yuburoll/DASIC/V2-375u/images/dasicHeader.jpg

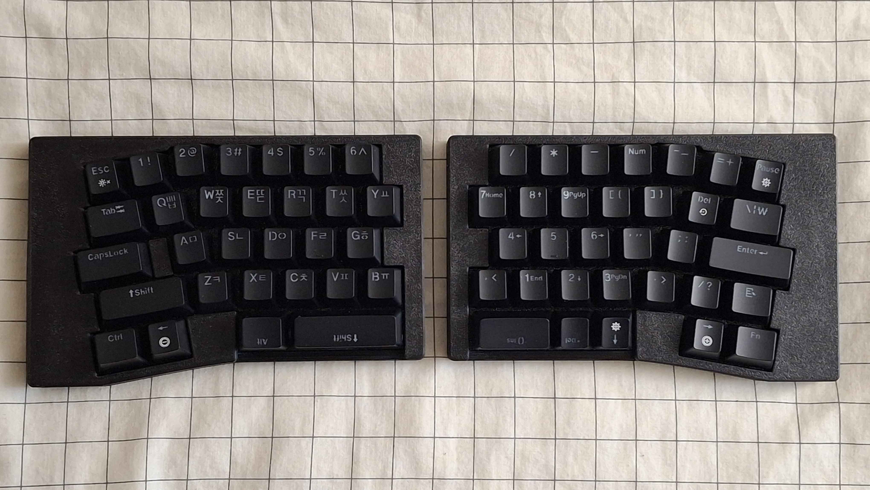
V2-375u/images/dasicHeader.jpg
