yuburoll/DASIC/V2-375u/images/dasicProfile.jpg

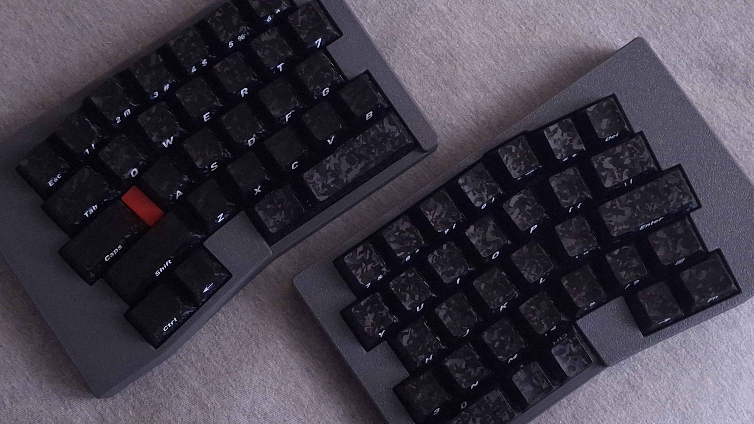
V2-375u/images/dasicProfile.jpg
