yuburoll/DASIC/V2-375u/images/dasicV2Pad.png

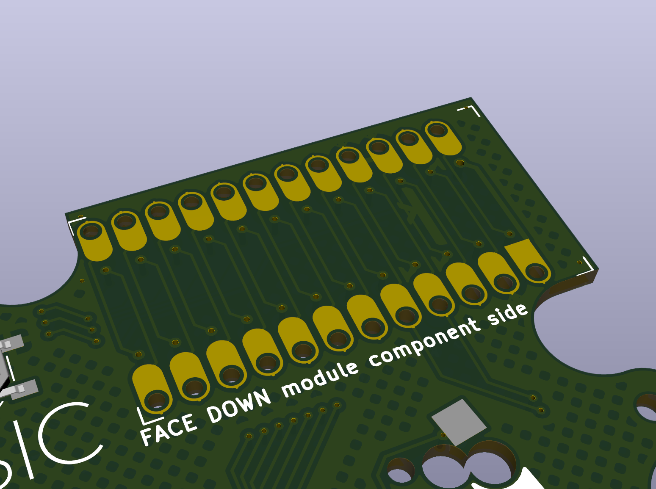
V2-375u/images/dasicV2Pad.png
