yuburoll/DASIC/V2-375u/kicad/dasic.kicad_sch

## KiCad design V2-375u/kicad/dasic.kicad_sch (2026-03-04)

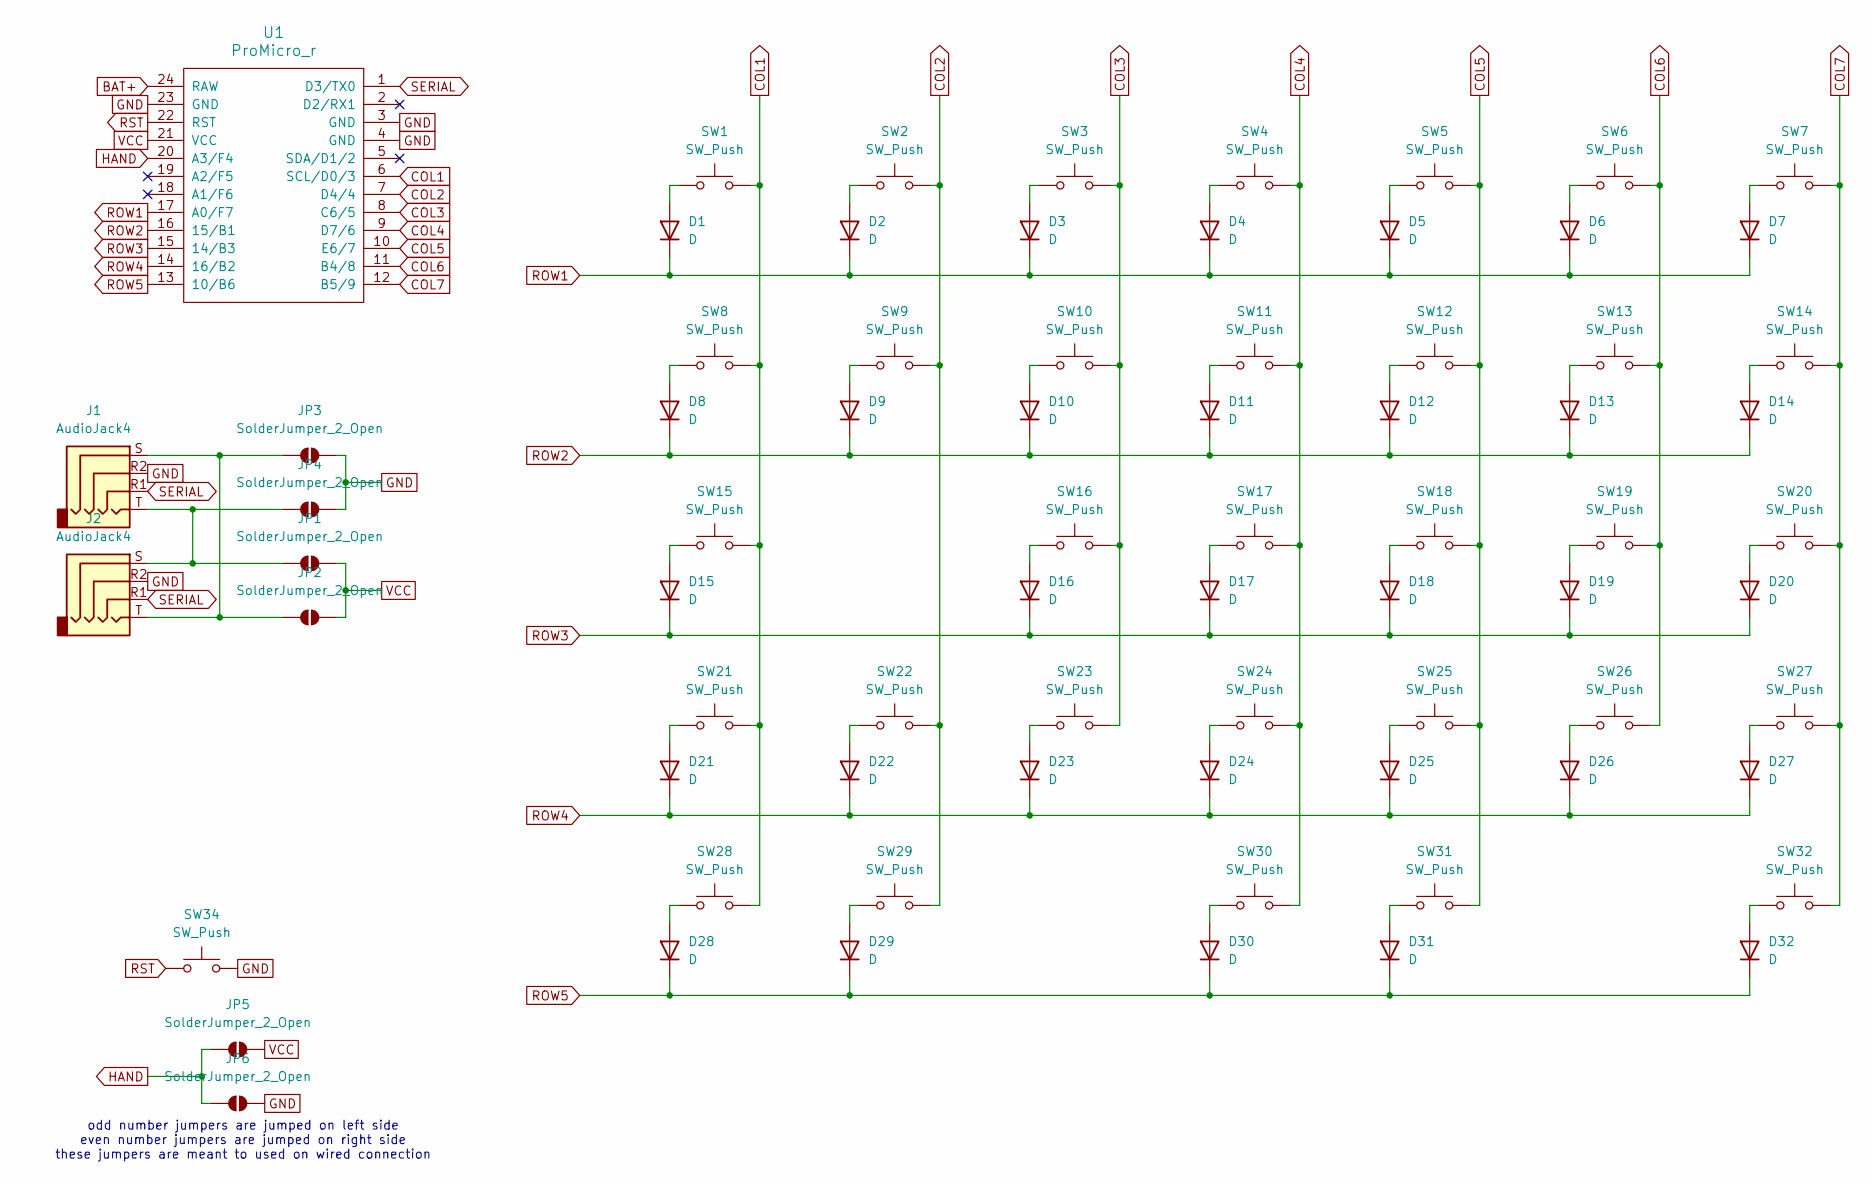
[picture p60: schematic dasic.kicad_sch]

Parts:
D1, D2, D3, D4, D5, D6, D7, D8, D9, D10, D11, D12, D13, D14, D15, D16, D17, D18, D19, D20, D21, D22, D23, D24, D25, D26, D27, D28, D29, D30, D31, D32: D
J1, J2: AudioJack4
JP1, JP2, JP3, JP4, JP5, JP6: SolderJumper_2_Open
SW1, SW2, SW3, SW4, SW5, SW6, SW7, SW8, SW9, SW10, SW11, SW12, SW13, SW14, SW15, SW16, SW17, SW18, SW19, SW20, SW21, SW22, SW23, SW24, SW25, SW26, SW27, SW28, SW29, SW30, SW31, SW32, SW34: SW_Push
U1: ProMicro_r

Connections:
BAT+: U1.24 (RAW)
COL1: SW1.2, SW8.2, SW15.2, SW21.2, SW28.2, U1.6 (SCL/D0/3)
COL2: SW2.2, SW9.2, SW22.2, SW29.2, U1.7 (D4/4)
COL3: SW3.2, SW10.2, SW16.2, SW23.2, U1.8 (C6/5)
COL4: SW4.2, SW11.2, SW17.2, SW24.2, SW30.2, U1.9 (D7/6)
COL5: SW5.2, SW12.2, SW18.2, SW25.2, SW31.2, U1.10 (E6/7)
COL6: SW6.2, SW13.2, SW19.2, SW26.2, U1.11 (B4/8)
COL7: SW7.2, SW14.2, SW20.2, SW27.2, SW32.2, U1.12 (B5/9)
GND: J1.R2, J2.R2, JP3.2 (B), JP4.2 (B), JP6.1 (A), SW34.2, U1.3 (GND), U1.4 (GND), U1.23 (GND)
HAND: JP5.2 (B), JP6.2 (B), U1.20 (A3/F4)
unnamed: D1.2 (A), SW1.1
unnamed: D2.2 (A), SW2.1
unnamed: D3.2 (A), SW3.1
unnamed: D4.2 (A), SW4.1
unnamed: D5.2 (A), SW5.1
unnamed: D6.2 (A), SW6.1
unnamed: D7.2 (A), SW7.1
unnamed: D8.2 (A), SW8.1
unnamed: D9.2 (A), SW9.1
unnamed: D10.2 (A), SW10.1
unnamed: D11.2 (A), SW11.1
unnamed: D12.2 (A), SW12.1
unnamed: D13.2 (A), SW13.1
unnamed: D14.2 (A), SW14.1
unnamed: D15.2 (A), SW15.1
unnamed: D16.2 (A), SW16.1
unnamed: D17.2 (A), SW17.1
unnamed: D18.2 (A), SW18.1
unnamed: D19.2 (A), SW19.1
unnamed: D20.2 (A), SW20.1
unnamed: D21.2 (A), SW21.1
unnamed: D22.2 (A), SW22.1
unnamed: D23.2 (A), SW23.1
unnamed: D24.2 (A), SW24.1
unnamed: D25.2 (A), SW25.1
unnamed: D26.2 (A), SW26.1
unnamed: D27.2 (A), SW27.1
unnamed: D28.2 (A), SW28.1
unnamed: D29.2 (A), SW29.1
unnamed: D30.2 (A), SW30.1
unnamed: D31.2 (A), SW31.1
unnamed: D32.2 (A), SW32.1
unnamed: J1.S, J2.T, JP2.1 (A), JP3.1 (A)
unnamed: J1.T, J2.S, JP1.1 (A), JP4.1 (A)
ROW1: D1.1 (K), D2.1 (K), D3.1 (K), D4.1 (K), D5.1 (K), D6.1 (K), D7.1 (K), U1.17 (A0/F7)
ROW2: D8.1 (K), D9.1 (K), D10.1 (K), D11.1 (K), D12.1 (K), D13.1 (K), D14.1 (K), U1.16 (15/B1)
ROW3: D15.1 (K), D16.1 (K), D17.1 (K), D18.1 (K), D19.1 (K), D20.1 (K), U1.15 (14/B3)
ROW4: D21.1 (K), D22.1 (K), D23.1 (K), D24.1 (K), D25.1 (K), D26.1 (K), D27.1 (K), U1.14 (16/B2)
ROW5: D28.1 (K), D29.1 (K), D30.1 (K), D31.1 (K), D32.1 (K), U1.13 (10/B6)
RST: SW34.1, U1.22 (RST)
SERIAL: J1.R1, J2.R1, U1.1 (D3/TX0)
VCC: JP1.2 (B), JP2.2 (B), JP5.1 (A), U1.21 (VCC)

Notes on the sheet:
odd number jumpers are jumped on left side even number jumpers are jumped on right side these jumpers are meant to used on wired connection
